jhrg/nixie-3/hv-ps-docs/n3-turn-off-time.png

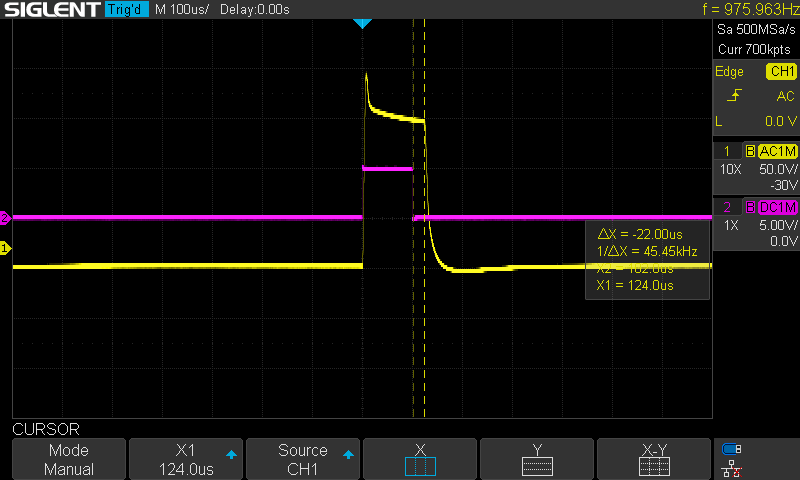
hv-ps-docs/n3-turn-off-time.png
