jhrg/nixie-3/hv-ps-docs/nixie-3-on-voltage.png

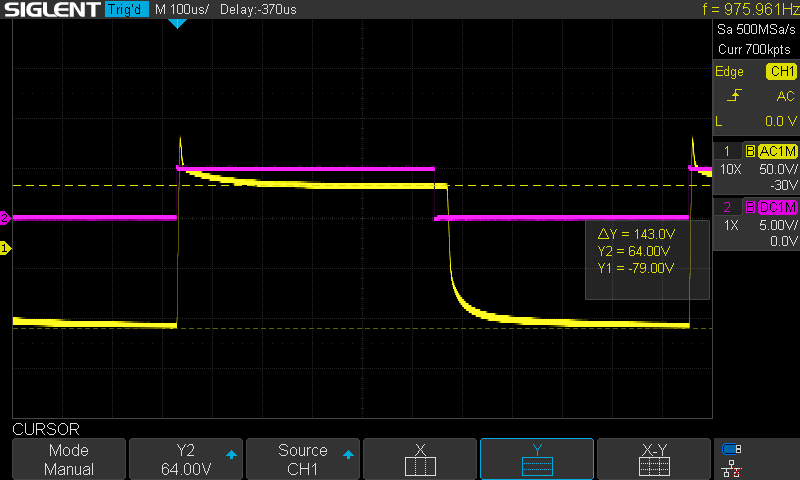
hv-ps-docs/nixie-3-on-voltage.png
