jhrg/nixie-3/hv-ps-docs/nixie-3-turn-off-time-w-gnd.png

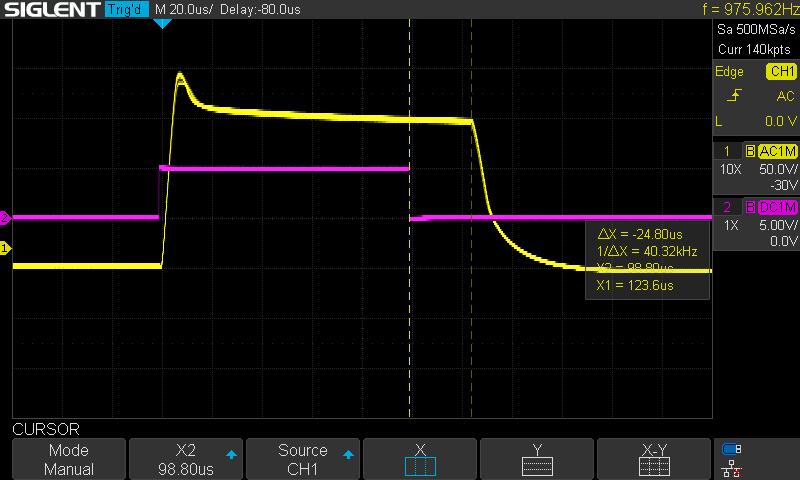
hv-ps-docs/nixie-3-turn-off-time-w-gnd.png
