jhrg/nixie-3/hv-ps-docs/nixie-3-turn-on-time-w-gnd.png

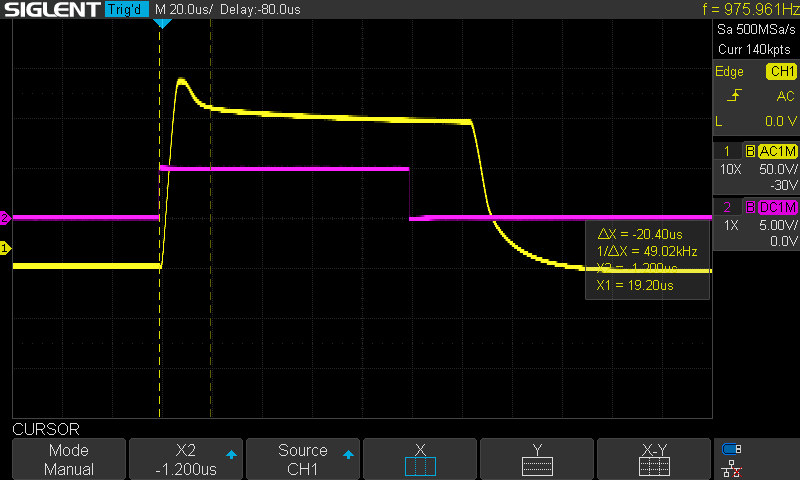
hv-ps-docs/nixie-3-turn-on-time-w-gnd.png
