jhrg/nixie-3/PCB/555-HV-PS/images/12MHz-ring-in-output.png

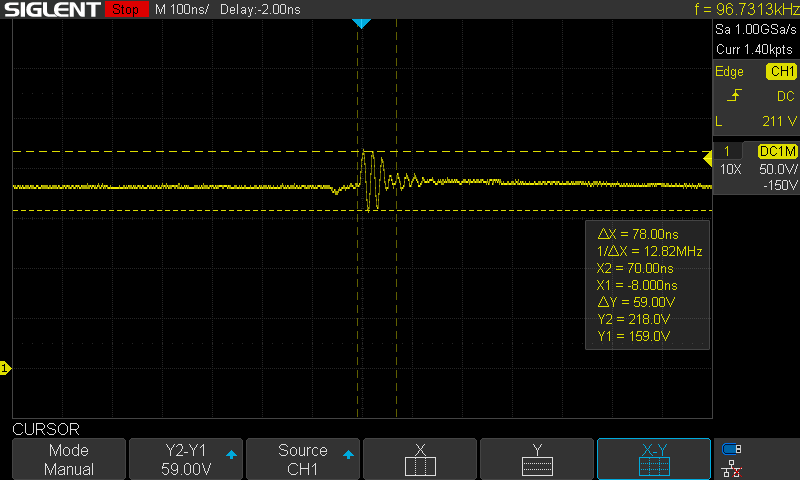
PCB/555-HV-PS/images/12MHz-ring-in-output.png
