jhrg/nixie-3/PCB/555-HV-PS/images/140v.png

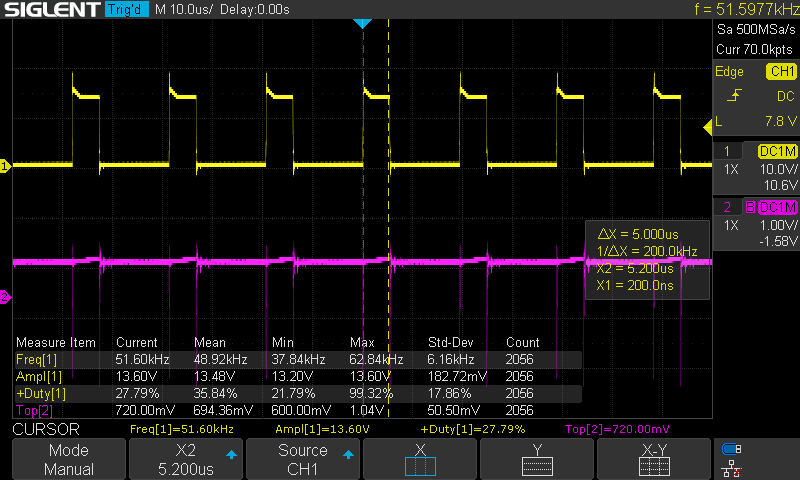
PCB/555-HV-PS/images/140v.png
