jhrg/nixie-3/PCB/555-HV-PS/images/555-HV-PS-2-timing.png

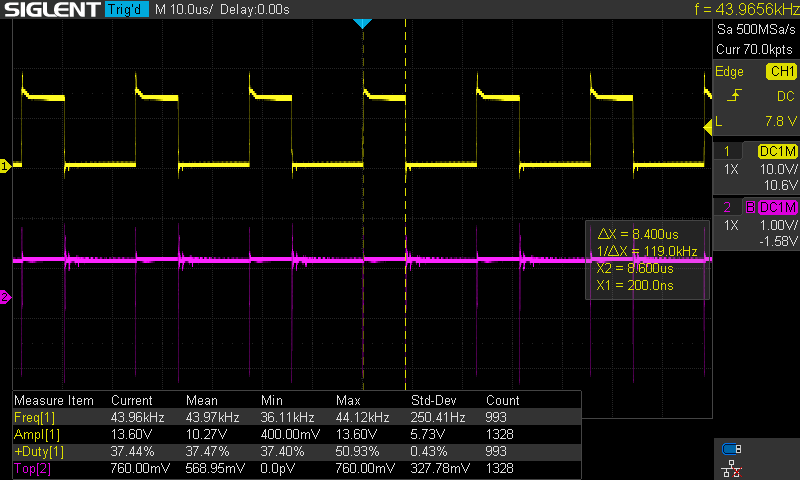
PCB/555-HV-PS/images/555-HV-PS-2-timing.png
