jhrg/nixie-3/PCB/555-HV-PS/images/555-HV-PS-turn-on-overshoot-1.png

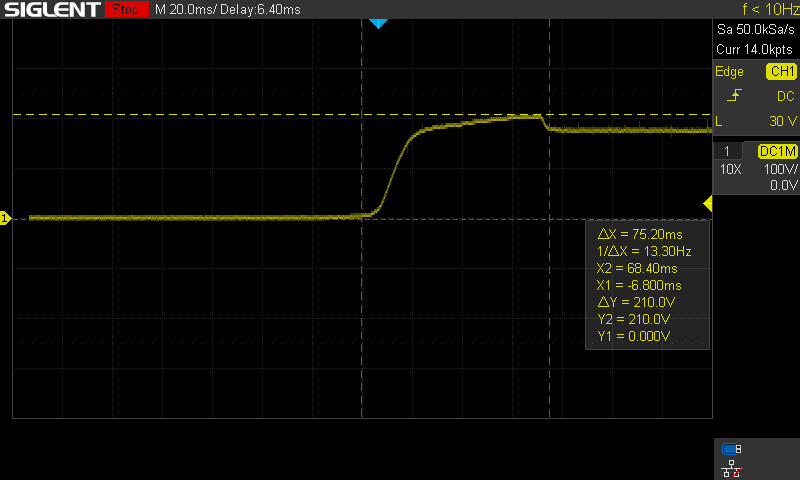
PCB/555-HV-PS/images/555-HV-PS-turn-on-overshoot-1.png
