jhrg/nixie-3/PCB/555-HV-PS/images/555-HV-PS-with-snubber.png

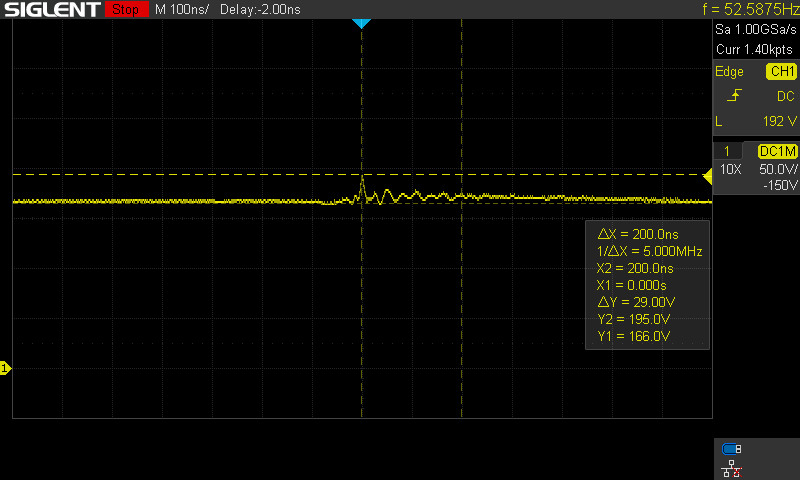
PCB/555-HV-PS/images/555-HV-PS-with-snubber.png
