jhrg/nixie-3/PCB/555-HV-PS/images/Inductor-voltage-w-cap.png

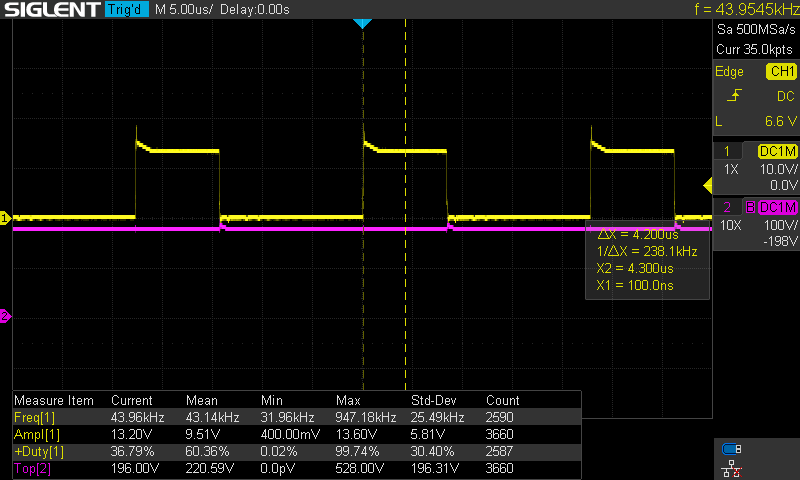
PCB/555-HV-PS/images/Inductor-voltage-w-cap.png
