jhrg/nixie-3/PCB/555-HV-PS/images/Inductor_voltage-wout-cap.png

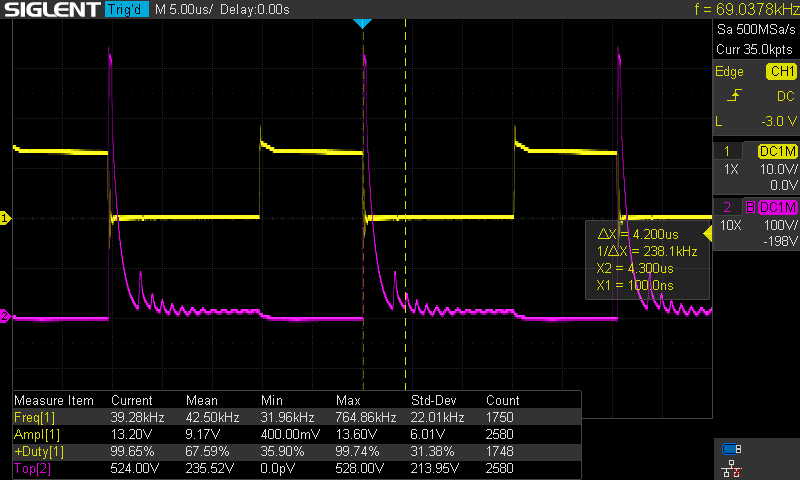
PCB/555-HV-PS/images/Inductor_voltage-wout-cap.png
