jhrg/nixie-3/PCB/555-HV-PS/images/RC-snubber/RC-snub-100pF-1K-output.png

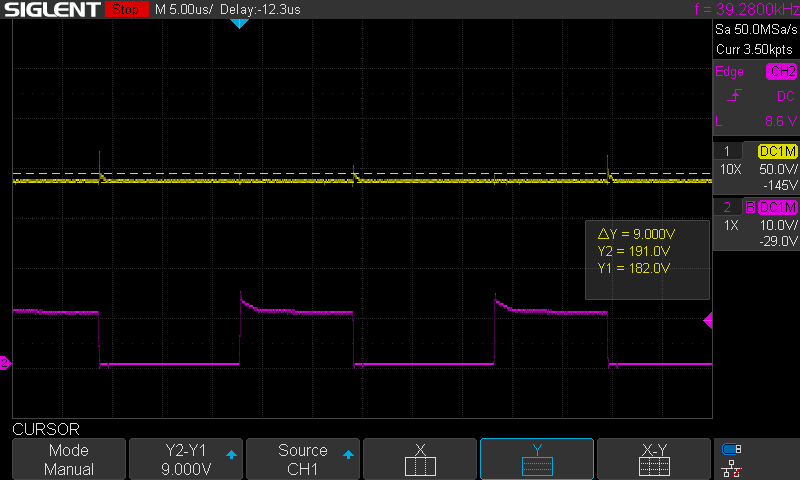
PCB/555-HV-PS/images/RC-snubber/RC-snub-100pF-1K-output.png
