jhrg/nixie-3/PCB/555-HV-PS/images/RC-snubber/RC-snub-470pF-1k-output-detail.png

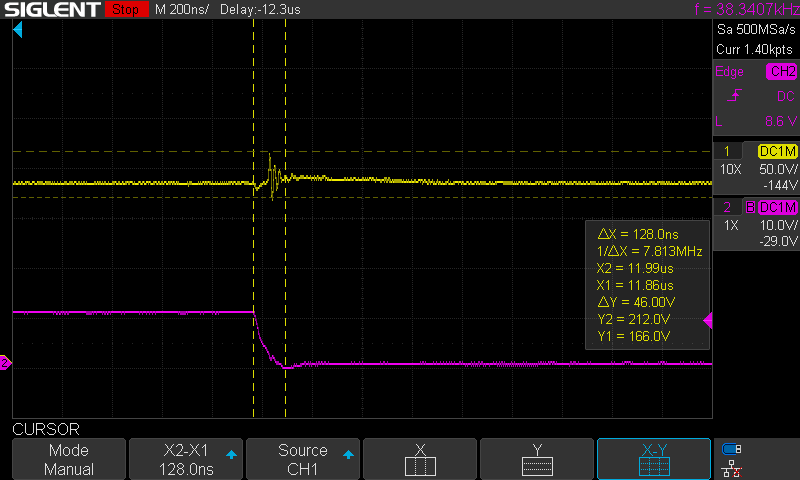
PCB/555-HV-PS/images/RC-snubber/RC-snub-470pF-1k-output-detail.png
