jhrg/nixie-3/include/mode_switch2.h

#ifndef mode_switch_h_
#define mode_switch_h_

enum switch_press_duration {
    none,
    quick,      // momentary
    medium_2s,  // 2s
    long_5s     // 5s
};

enum display_mode {
    mm_ss,
    hh_mm
};

enum switch_press_duration read_button_1();
enum switch_press_duration read_button_2();
void mode_switch_setup();

/**
 * @brief Toggle between the two display modes (MM:SS <-> HH:MM).
 */
enum display_mode toggle_display_mode(enum display_mode display_mode);

#endif
